KshitijKulkarni/Project-Arka/Circuits/EthernetPCB/Screenshot 2026-02-04 032121.png

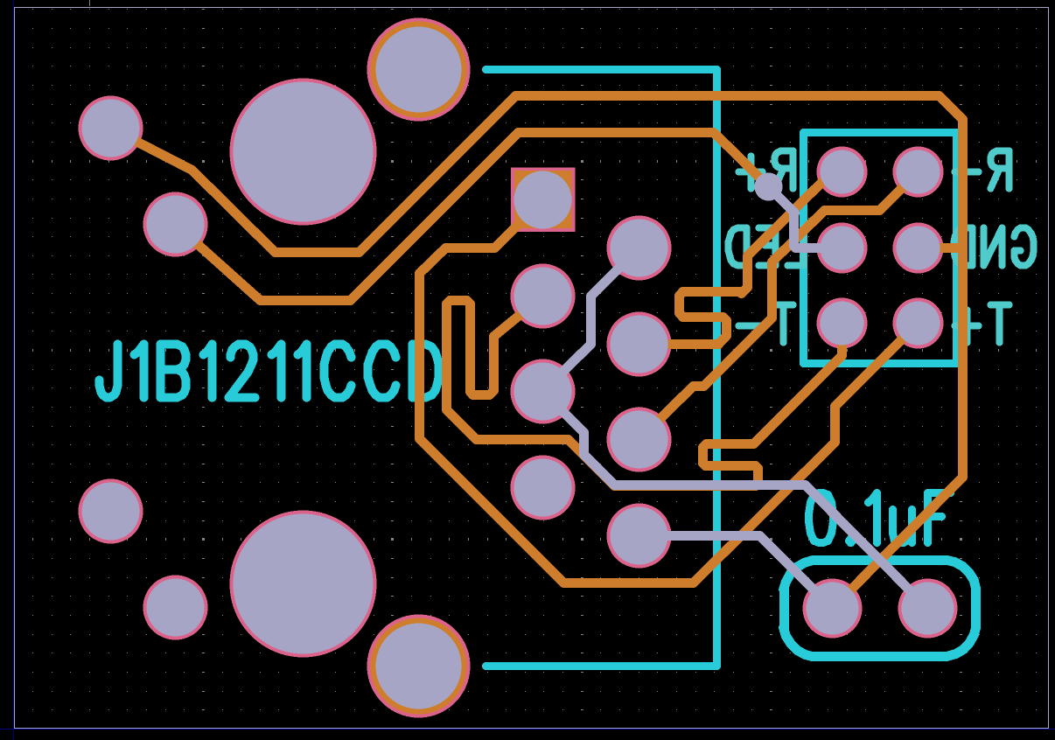
Circuits/EthernetPCB/Screenshot 2026-02-04 032121.png
