KshitijKulkarni/Project-Arka/Ground Control Code/Temporary File Dump/BG.png

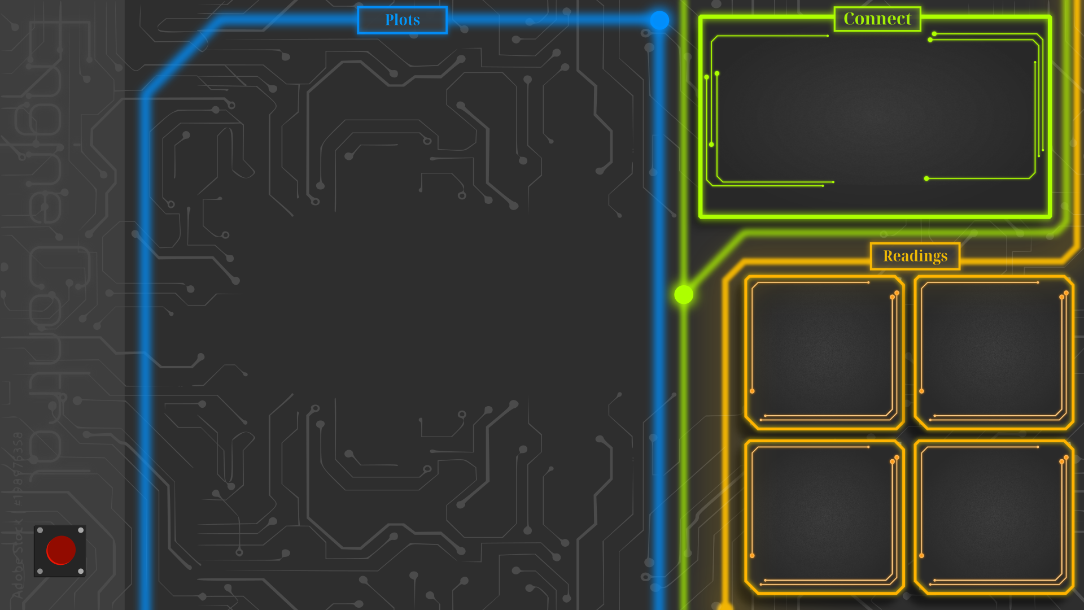
Ground Control Code/Temporary File Dump/BG.png
