KshitijKulkarni/Project-Arka/Microcontroller Code/Guru/include/DataStructs.h

#ifndef DATASTRUCTS_H
#define DATASTRUCTS_H

#include <Arduino.h>

struct OldGyan {
    uint8_t rpm; //id - 0xA0
    uint16_t thrust; //id - 0xB0
    uint8_t flow; //id - 0xC0
    uint16_t pressure[4]; //id - 0xD0
    uint16_t temperature[9]; //id - 0xE0
    // Total 30 bytes
    // Status should also be included in the future
};

struct Gyan {
    uint64_t timestamp;
    uint8_t rpm; //id - 0xA0
    uint32_t thrust; //id - 0xB0
    uint64_t currFlow; //id - 0xC0
    uint64_t setFlow;
    int32_t pressure[4]; //id - 0xD0
    uint32_t temperature[9]; //id - 0xE0
    uint8_t status;
    // Total 82 bytes
};

struct Directive {
    uint8_t id; //0xAA - SetFlowRate, 0xAB - switchSatus
    uint16_t value;
    // Total 3 bytes
};

struct TargetState {
    uint8_t state;
    uint16_t targetFlow;
};

/*
struct LogStruct {
    
};
*/

#endif
